alex-v999/digital-farming-hydroponics/Pictures/Blender - Prototype (1).png

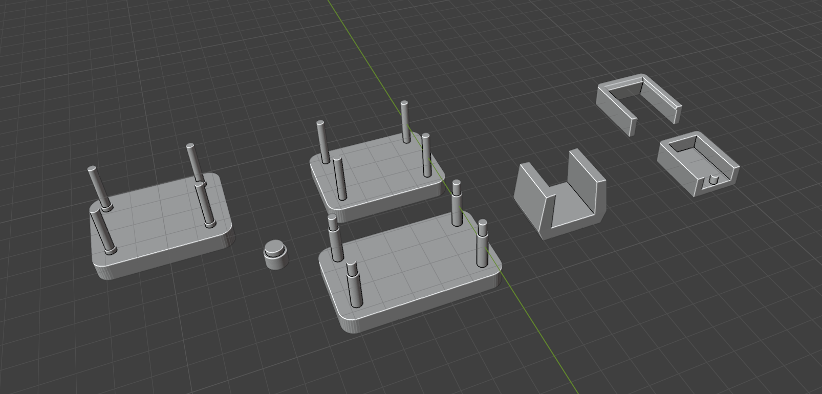
Pictures/Blender - Prototype (1).png
