alex-v999/digital-farming-hydroponics/Pictures/Blender - Prototype (2).png

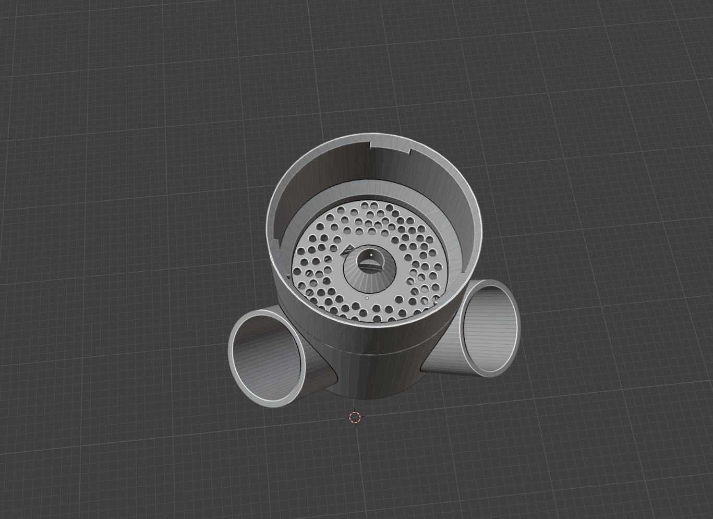
Pictures/Blender - Prototype (2).png
