alex-v999/digital-farming-hydroponics/Pictures/Blender - Prototype (4).png

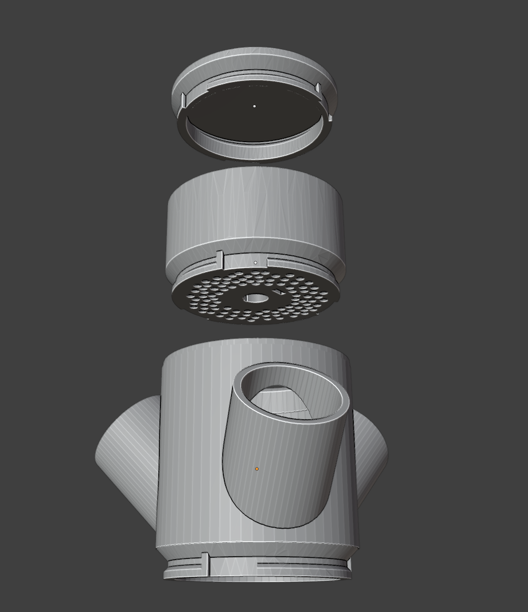
Pictures/Blender - Prototype (4).png
