alex-v999/digital-farming-hydroponics/Pictures/REAL LIFE PICTURES (1).jpg

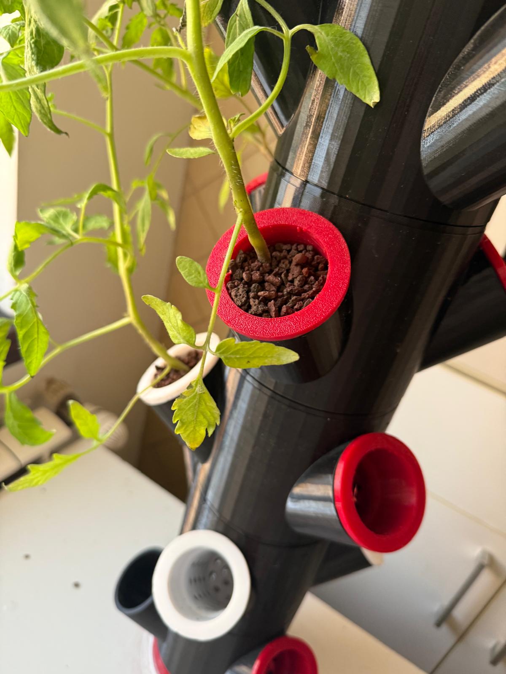
Pictures/REAL LIFE PICTURES (1).jpg
